kushima8/Reex/STL/reexmod_5key_spacer.stl

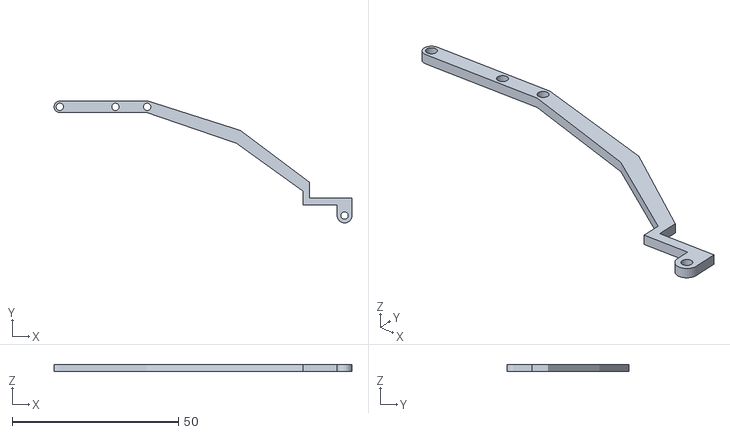
[picture p15: CAD file, 2026-07-12]
STL/reexmod_5key_spacer.stl
89.6 x 36.7 x 2.00
