kushima8/Reex/STL/reex_2.5-3.5_spacer.stl

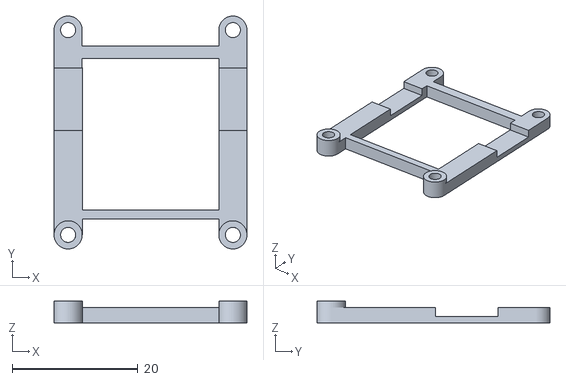
[picture p16: CAD file, 2026-07-12]
STL/reex_2.5-3.5_spacer.stl
30.7 x 37.1 x 3.50
