kushima8/Reex/STL/reex_cover_oled.stl

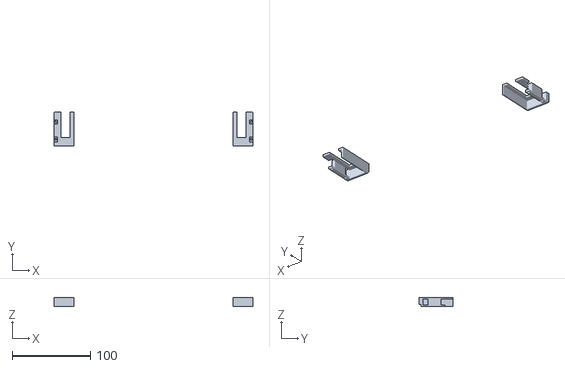
[picture p17: CAD file, 2026-07-12]
STL/reex_cover_oled.stl
253.6 x 42.7 x 11.5
