kushima8/Reex/STL/reex_3.5_stick_spacer.stl

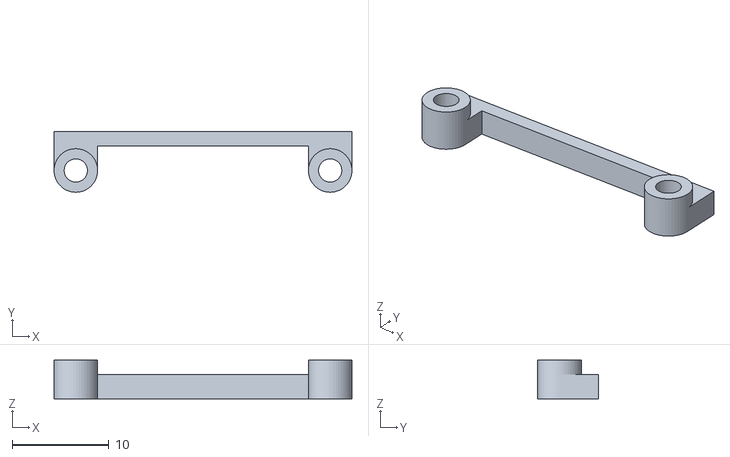
[picture p18: CAD file, 2026-07-12]
STL/reex_3.5_stick_spacer.stl
30.7 x 6.25 x 4.00
