kushima8/Reex/BreakoutBoard/PCB/breakoutboard_base/breakoutboard.sch

## KiCad design BreakoutBoard/PCB/breakoutboard_base/breakoutboard.sch (2023-05-31)

Schematic: breakoutboard.sch

Parts:
J1, J2, J3, J4: Conn_01x08; PinHeader_1x08_P2.54mm_Vertical
